thisisdibbo/ESP32-PM-Sensor/images/First_Design_2.png

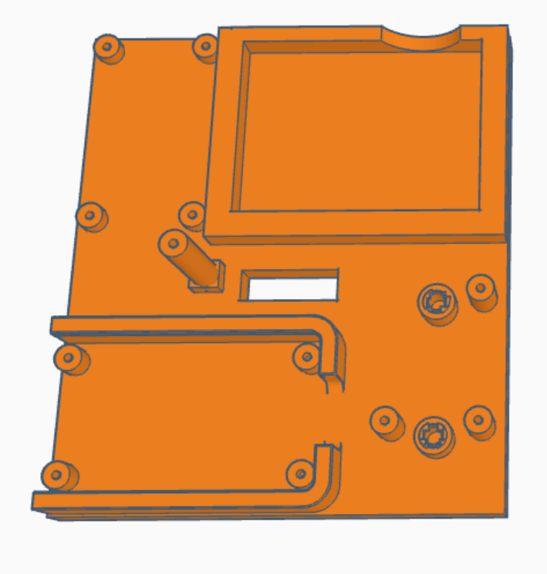
images/First_Design_2.png
