thisisdibbo/ESP32-PM-Sensor/images/PCB_Schematic.png

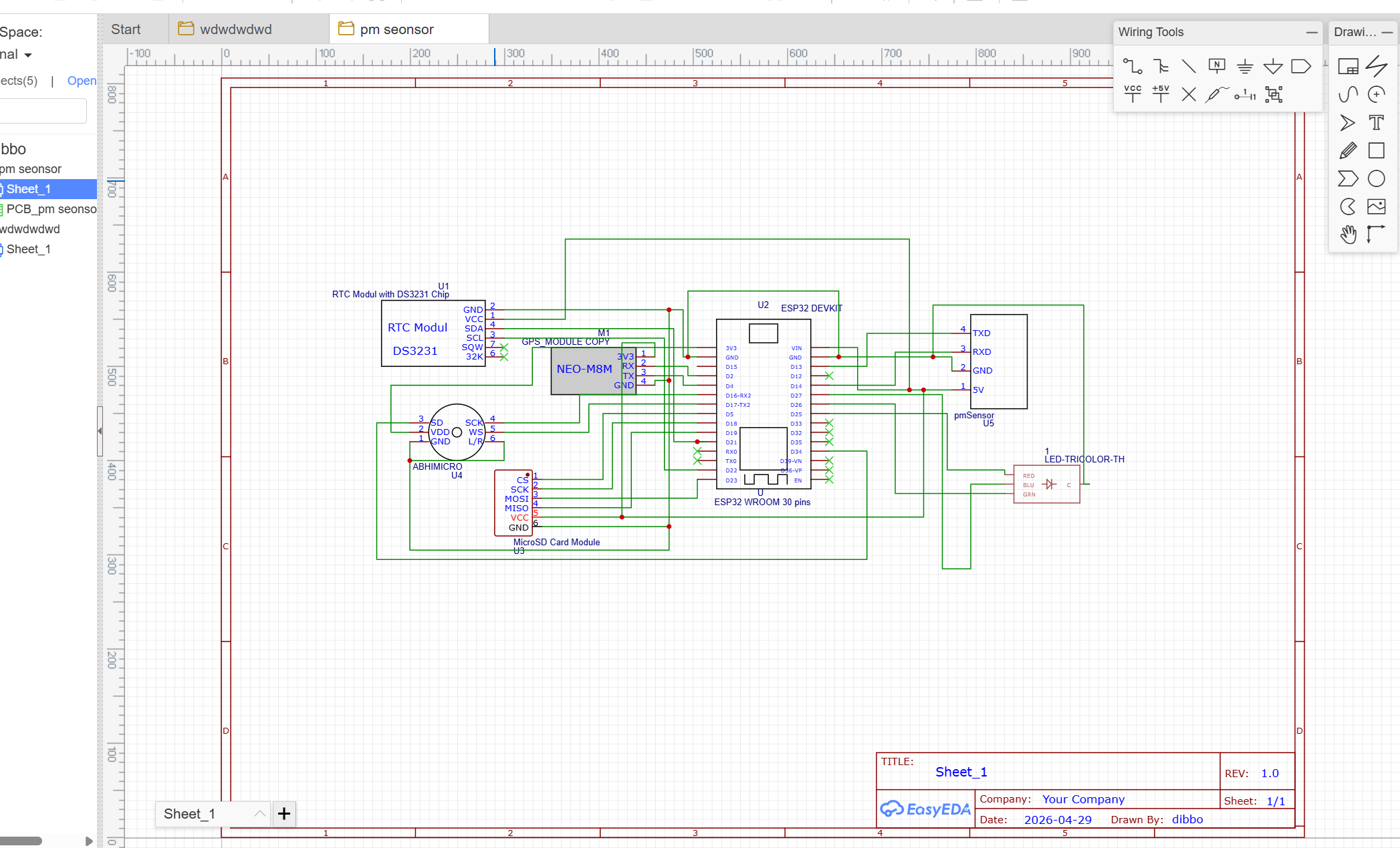
images/PCB_Schematic.png
